anuvgupta/led-lights/ios_client/ios_d_colors.png

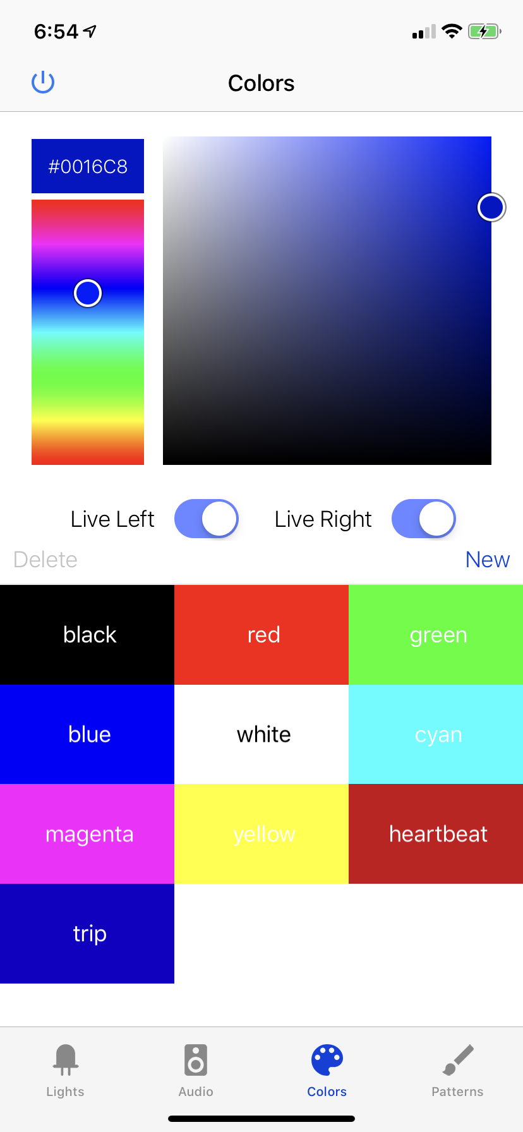
ios_client/ios_d_colors.png
