anuvgupta/led-lights/ios_client/ios_a_lights.png

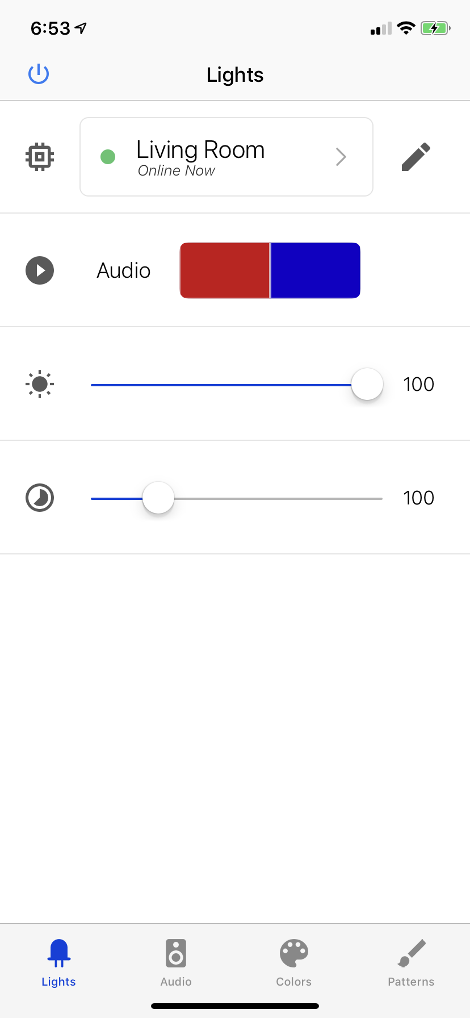
ios_client/ios_a_lights.png
