anuvgupta/led-lights/ios_client/ios_b_devices.png

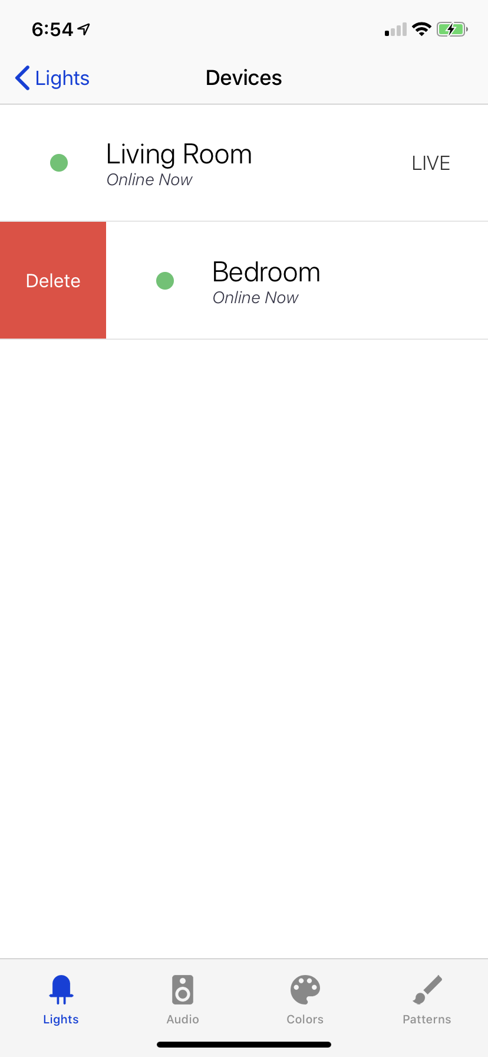
ios_client/ios_b_devices.png
