anuvgupta/led-lights/ios_client/ios_c_audio.png

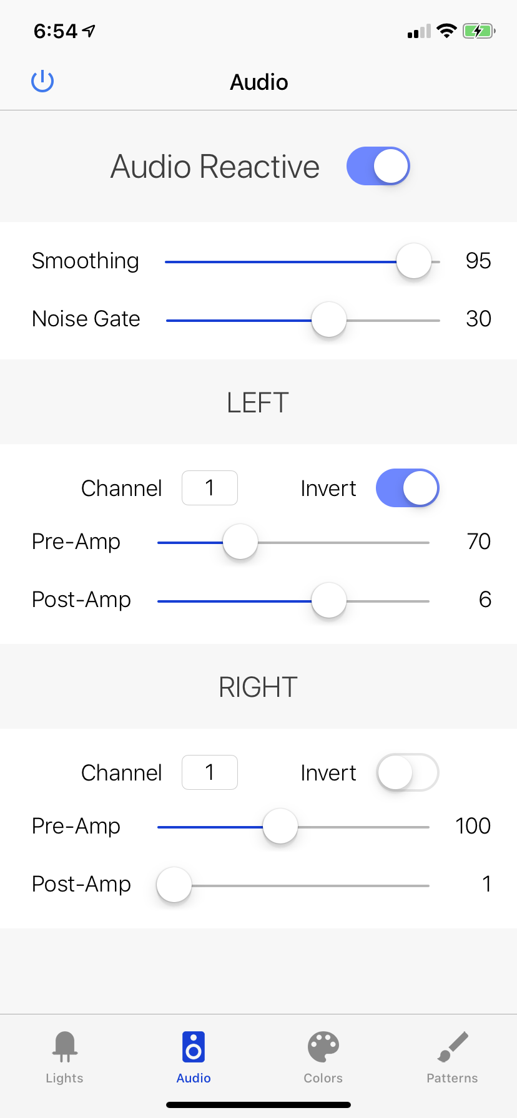
ios_client/ios_c_audio.png
