anuvgupta/led-lights/ios_client/ios_e_patterns.png

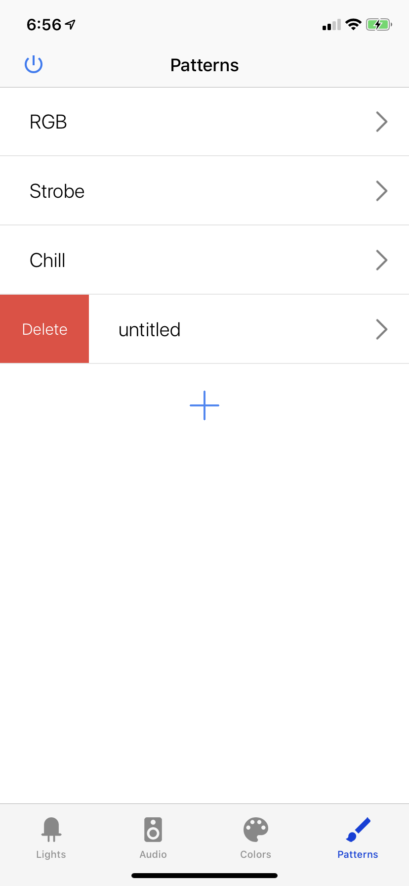
ios_client/ios_e_patterns.png
