anuvgupta/led-lights/ios_client/ios_f_pattern_edit.png

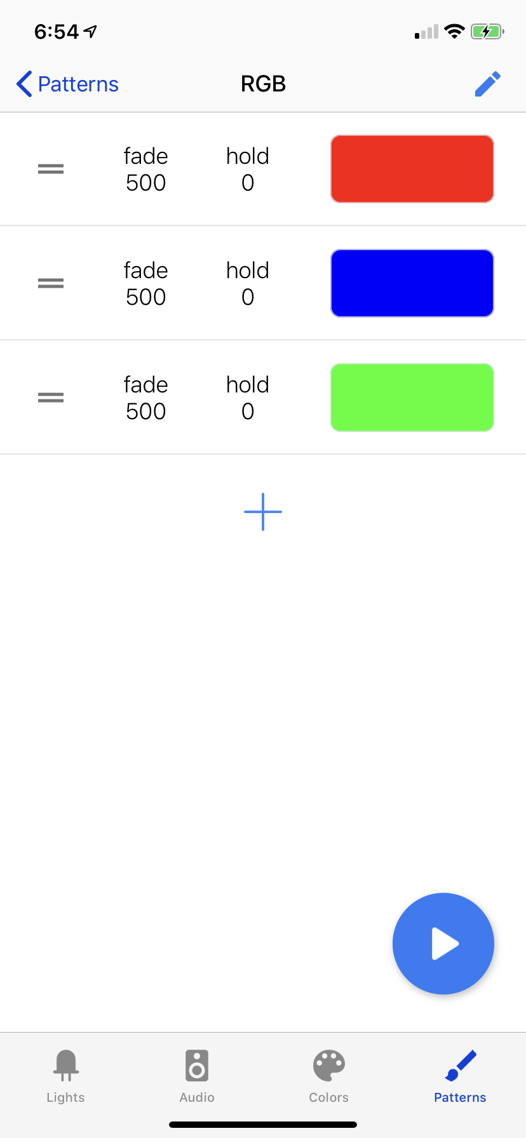
ios_client/ios_f_pattern_edit.png
