anuvgupta/led-lights/ios_client/ios_g_color_select.png

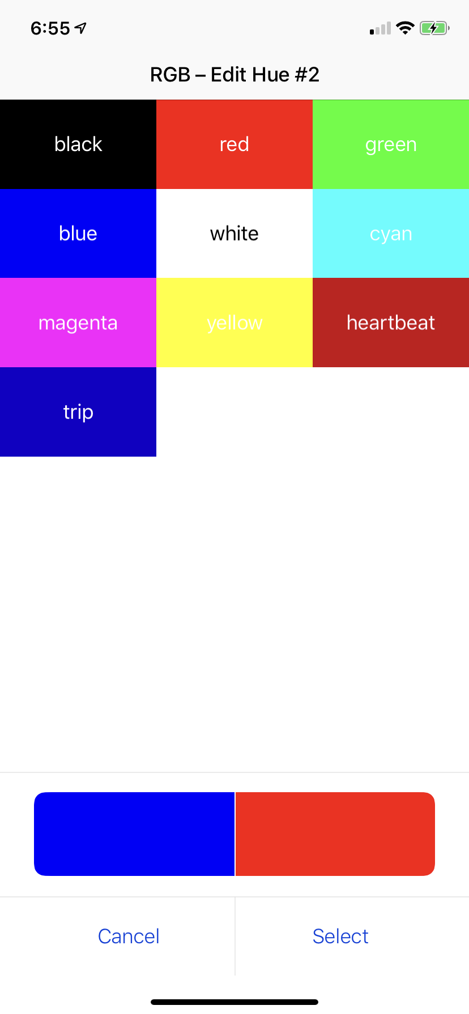
ios_client/ios_g_color_select.png
