anuvgupta/led-lights/nodejs_server/html/img/exit_w.png

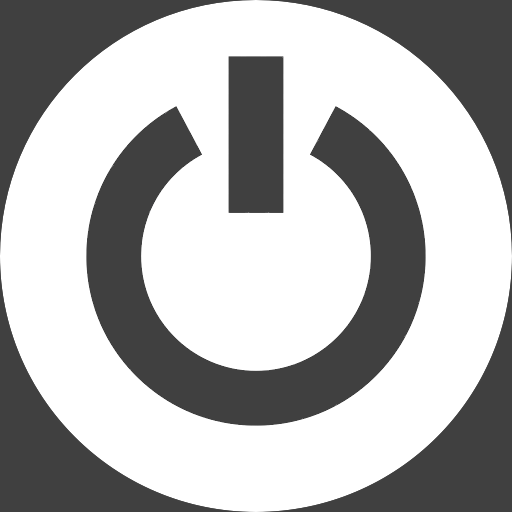
nodejs_server/html/img/exit_w.png
