anuvgupta/led-lights/arduino_esp8266/esp_ws_client/secrets.h

#define SECRET_SSID "ssid"
#define SECRET_PASS "pass"
#define SECRET_AUTH_JSON "{\"event\":\"auth\",\"data\":{\"password\":\"control\"}}"
#define DEVICE_SYNC_JSON "{\"event\":\"arduino_sync\",\"data\":\"device1\"}"
char secret_ssid[11] = SECRET_SSID;
